lab11/permamote/software/apps/permacam/camera_quality/README.md

Camera Qualities Test
===============

Send the same image in multiple jpeg qualities and raw
