lab11/permamote/software/apps/permacam/spi_peripheral_test/README.md

Camera Test
===============

Try to get camera working
