lab11/permamote/software/apps/permamote_coap/permamote_coap.h

#pragma once
#include "time.h"
#include "simple_thread.h"
#include "thread_coap.h"
#include "app_error.h"

#include "parse.pb.h"

#define PERMAMOTE_PACKET_VERSION 3

typedef struct {
  char* path;
  uint8_t id_len;
  uint8_t* id;
  uint32_t seq_no;
  struct timeval timestamp;
  uint8_t data_len;
  uint8_t* data;
} permamote_packet_t;

otError permamote_coap_send(otIp6Address* dest, const char* path, bool confirmable, Message* msg);
